jgraichen/someline/export/someline-36/U7.step

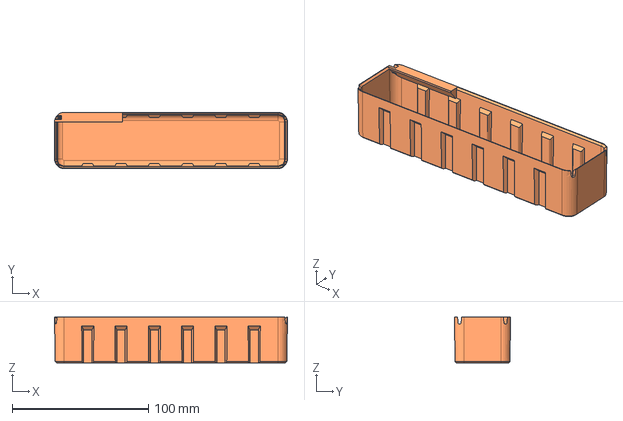
[picture p24: CAD file, 2026-08-25]
export/someline-36/U7.step
170.8 x 41.2 x 33.7 mm
