jgraichen/someline/export/someline-15/U0.step

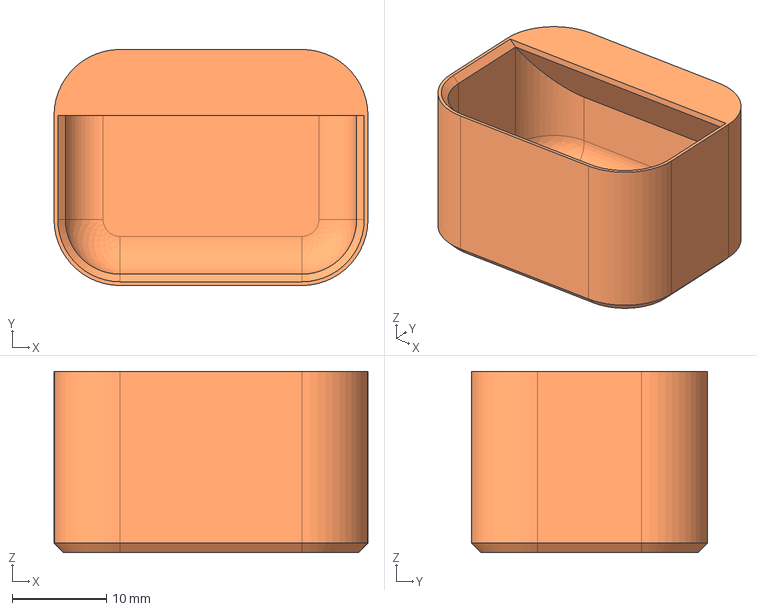
[picture p25: CAD file, 2026-06-25]
export/someline-15/U0.step
33.2 x 25.0 x 19.2 mm
