jgraichen/someline/export/someline-36/U10.step

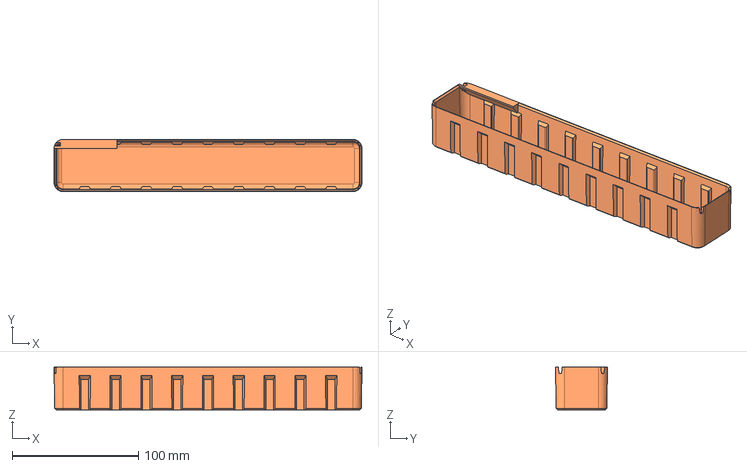
[picture p26: CAD file, 2026-08-25]
export/someline-36/U10.step
244.0 x 41.2 x 33.7 mm
