jgraichen/someline/export/someline-15/U5.step

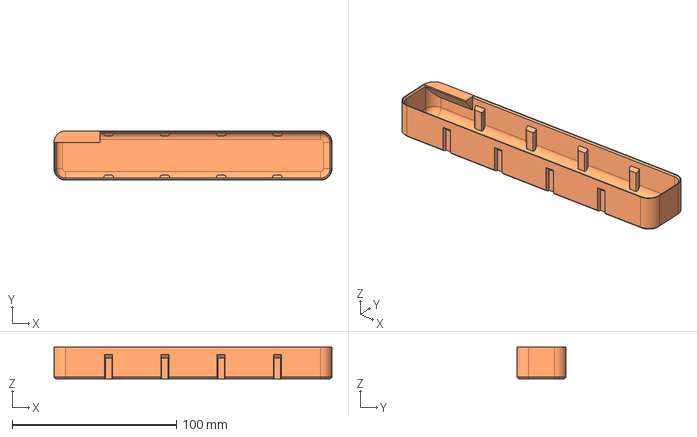
[picture p27: CAD file, 2026-06-25]
export/someline-15/U5.step
169.2 x 30.0 x 19.2 mm
