jgraichen/someline/export/someline-36/U3.step

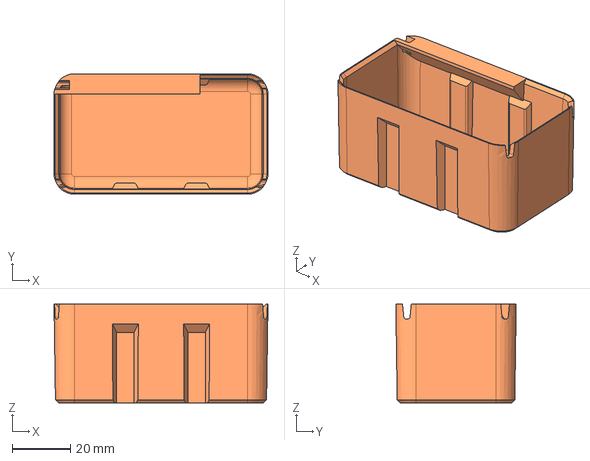
[picture p28: CAD file, 2026-08-25]
export/someline-36/U3.step
73.2 x 41.2 x 33.7 mm
