jgraichen/someline/export/someline-36/U6.step

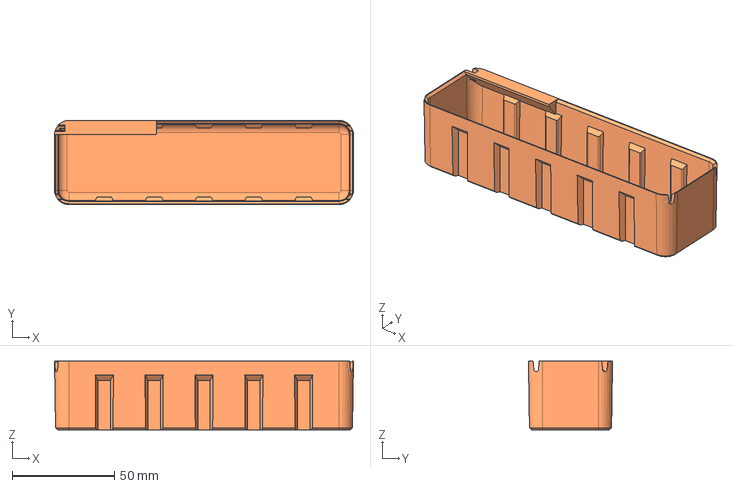
[picture p29: CAD file, 2026-08-25]
export/someline-36/U6.step
146.4 x 41.2 x 33.7 mm
