jgraichen/someline/export/someline-36/B2.step

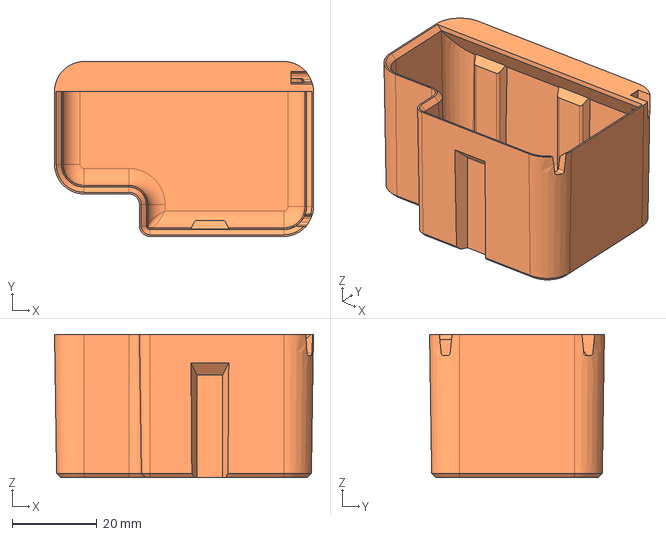
[picture p30: CAD file, 2026-06-25]
export/someline-36/B2.step
61.0 x 41.2 x 33.7 mm
