jgraichen/someline/export/someline-36/B1.step

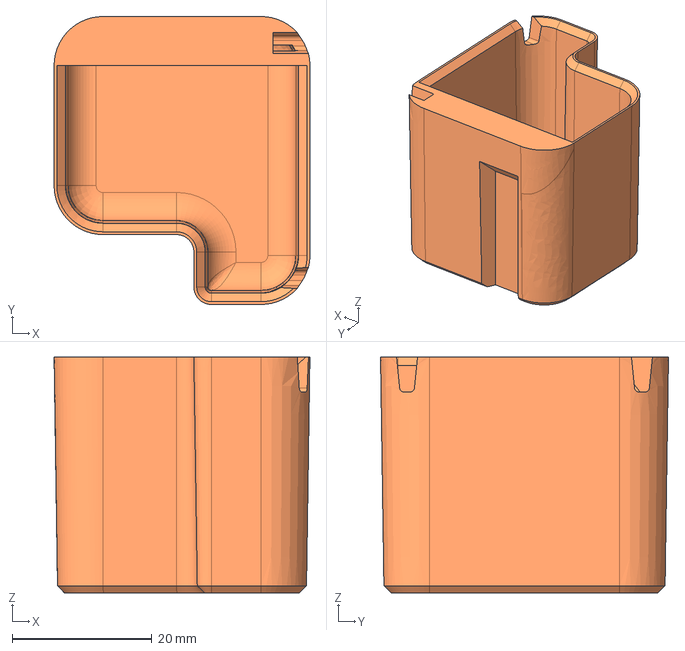
[picture p31: CAD file, 2026-06-25]
export/someline-36/B1.step
36.6 x 41.2 x 33.7 mm
