jgraichen/someline/export/someline-36/U2.step

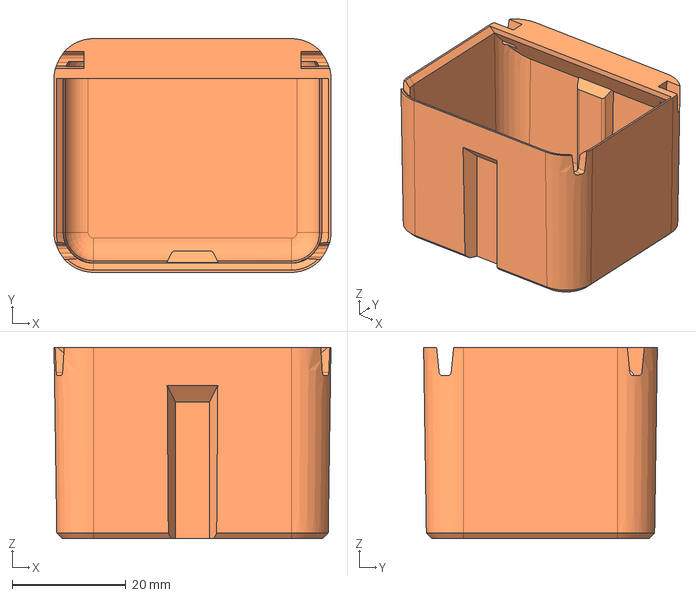
[picture p32: CAD file, 2026-06-25]
export/someline-36/U2.step
48.8 x 41.2 x 33.7 mm
