jgraichen/someline/export/someline-36/C5.step

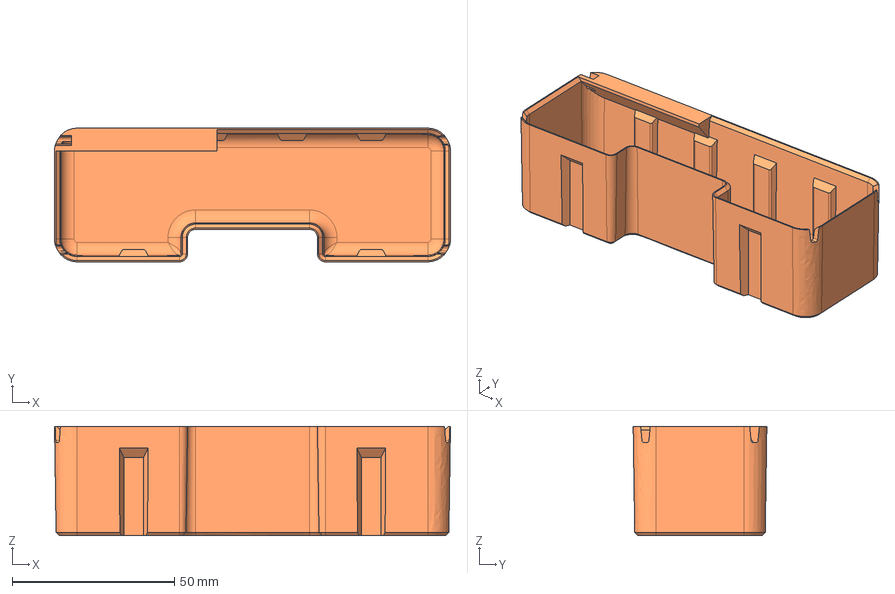
[picture p33: CAD file, 2026-06-25]
export/someline-36/C5.step
122.0 x 41.2 x 33.7 mm
