jgraichen/someline/export/someline-36/U1.step

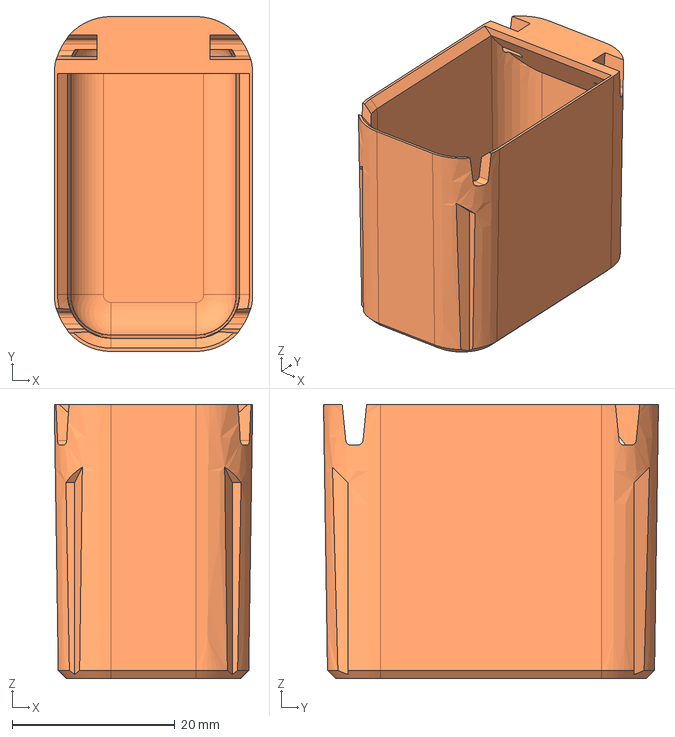
[picture p34: CAD file, 2026-06-25]
export/someline-36/U1.step
24.4 x 41.2 x 33.7 mm
